bachelor-2020/drone-kropp/chassis.scad

include <config/main_config.scad>

include <lego/lego.scad>
include <rpi/RPI.scad>
include <arduino/arduino.scad>
include <grideye/grideye.scad>

PLATE_THICKNESS = beamh;
padding = 17;
length = RPI_LENGTH + padding;
diagonal = sqrt(1/2) * length;
cutoff = 12;
radius = diagonal-cutoff;

module place_on_corners(distance=0){
	r = radius + distance;
	for (d = [0 : 90 : 360])
		rotate([0, 0, d+45])
		translate([0, r])
		children();
}

module sandwich_plate(){
	difference(){
		translate([0, 0, PLATE_THICKNESS/2])
			cube([length, length, PLATE_THICKNESS], center=true);

		// Cut off corners
		place_on_corners(length)
			cube(2*length, center=true);
	}
}

module grideye_mount_plate(bracket_length=1){
	place_on_corners()
		arm_bracket(bracket_length);
	difference(){
		sandwich_plate();
		grideye_screwholes();
		translate([0, 0, 2]) {
			grideye_cutout();
			scale([0.9, 0.9, 1.1])
				sandwich_plate();
		}
	}
}

module arduino_mount_plate(bracket_length=1){
	place_on_corners()
		arm_bracket(bracket_length);
	difference(){
		sandwich_plate();
		arduino_screwholes();
		translate([0, 0, 2]) {
			arduino_cutout();
			scale([0.9, 0.9, 1.1])
				sandwich_plate();
		}
	}

	if (PLACEHOLDERS)
		#translate([0, 0, 2])
		arduino();
}

module rpi_mount_plate(bracket_length=1){
	place_on_corners()
		arm_bracket(bracket_length);
	difference(){
		sandwich_plate();
		rpi_screwholes();
		translate([0, 0, 2]) {
			rpi_cutout();
			scale([0.9, 0.9, 1.1])
				sandwich_plate();
		}
	}

	if (PLACEHOLDERS)
		#translate([0, 0, 2])
		rpi();
}

module arm_plate(bracket_length=3){
	place_on_corners()
		arm_bracket(bracket_length);
	difference(){
		sandwich_plate();
		translate([0, 0, -0.1])
			scale([0.9, 0.9, 1.1])
			sandwich_plate();
	}
}


module arm_bracket(length=4){
	translate([-beamw/2, 0, beamw/2])
	rotate([0, 90, 0])
	difference(){
		translate([0, -beamw])
			beam(length+1);
		translate([-beamw/2, -beamw])
			cube(beamw);
	}
}

module arm_bracket_double(length=4){
	for (x = [-1,1]*beamw){
		translate([x, 0]) arm_bracket(length);
	}
}
